poor-charles/Distributed-IoT-Mechatronic-System-for-HVAC-Optimization-using-Hybrid-AI-Logic/Hardware System Files/Data Analysis/Smart_HVAC_Consumer_ROI_Payback.xlsx

Sheet: Consumer Inputs
Smart HVAC Controller Consumer-Side Assumptions
Input | Value | Unit | Purpose / Meanimgng
Electricity Rate | ₱10.5049 | Peso/kWh | Consumer tariff paid for HVAC electricity consumption in Year 1.
Electricity Rate Escalation | 9.0% | %/year | Expected yearly increase in electricity price.
Existing HVAC Annual Energy Consumption (Before Smart Controller) | 2261.15 | kWh/year | Measured or estimated Year 1 annual HVAC energy consumption under manual setpoint operation. The HVAC unit is not purchased; it already exists.
Annual HVAC Energy Consumption Variation | 2.0% | %/year | Expected yearly change in existing HVAC energy use due to weather, occupancy, operating hours, and equipment aging.
Measured Energy Savings Achieved by Smart HVAC Controller | 20.5% | % | Experimentally observed savings delivered by the controller; applied to each year's projected baseline HVAC consumption.
Smart HVAC Controller Package Cost | ₱26000 | Peso | One-time consumer cost for the controller package only. This does NOT include the HVAC unit.
Controller Installation & Setup Cost | ₱0 | Peso | One-time installation, configuration, and commissioning cost for the controller.
Smart Controller Annual Maintenance | ₱1389.4 | Peso/year | Recurring consumer-side operating cost. Enter 0 if none.
Smart Controller Useful Life | 12 | years | Expected service life of the Smart HVAC controller package.
Smart Controller Salvage Value | 0 | Peso | Residual value at the end of the controller useful life for depreciation calculation.

Sheet: Consumer Cash Flow
Consumer Cash Flow: Existing HVAC vs Smart HVAC Controller Purchase
Year | Electricity Rate | Manual HVAC kWh | Smart HVAC kWh | kWh Saved | Manual Bill | Smart Bill | Recurring Smart Cost | Net Annual Savings | Cumulative Net Cash Flow
0 | ₱0.0000 | - | - | - | - | - | - | -₱26000 | -₱26000
1 | ₱10.5049 | 2261.15 | 1796.718835 | 464.4311654 | ₱23753.15463 | ₱18874.35169 | ₱1389.4 | ₱3489.402949 | -₱22510.59705
2 | ₱11.4503 | 2306.373 | 1832.653211 | 473.7197887 | ₱26408.75732 | ₱20984.5042 | ₱1389.4 | ₱4034.853119 | -₱18475.74393
3 | ₱12.4809 | 2352.50046 | 1869.306276 | 483.1941845 | ₱29361.25639 | ₱23330.57177 | ₱1389.4 | ₱4641.284618 | -₱13834.45931
4 | ₱13.6042 | 2399.550469 | 1906.692401 | 492.8580682 | ₱32643.84486 | ₱25938.9297 | ₱1389.4 | ₱5315.515158 | -₱8518.944155
5 | ₱14.8285 | 2447.541479 | 1944.826249 | 502.7152295 | ₱36293.42671 | ₱28838.90204 | ₱1389.4 | ₱6065.124673 | -₱2453.819483
6 | ₱16.1631 | 2496.492308 | 1983.722774 | 512.7695341 | ₱40351.03182 | ₱32063.09129 | ₱1389.4 | ₱6898.540531 | ₱4444.721049
7 | ₱17.6178 | 2546.422154 | 2023.39723 | 523.0249248 | ₱44862.27718 | ₱35647.74489 | ₱1389.4 | ₱7825.132283 | ₱12269.85333
8 | ₱19.2034 | 2597.350597 | 2063.865174 | 533.4854233 | ₱49877.87976 | ₱39633.16277 | ₱1389.4 | ₱8855.316992 | ₱21125.17032
9 | ₱20.9317 | 2649.297609 | 2105.142478 | 544.1551318 | ₱55454.22672 | ₱44064.15037 | ₱1389.4 | ₱10000.67635 | ₱31125.84667
10 | ₱22.8155 | 2702.283562 | 2147.245327 | 555.0382344 | ₱61654.00927 | ₱48990.52238 | ₱1389.4 | ₱11274.08689 | ₱42399.93356
11 | ₱24.8689 | 2756.329233 | 2190.190234 | 566.1389991 | ₱68546.9275 | ₱54467.66278 | ₱1389.4 | ₱12689.86472 | ₱55089.79828
12 | ₱27.1071 | 2811.455817 | 2233.994038 | 577.4617791 | ₱76210.474 | ₱60557.14748 | ₱1389.4 | ₱14263.92652 | ₱69353.7248

Sheet: Consumer Scenarios
Consumer Adoption Scenarios
Scenario | Savings % | Electricity Rate | Year 1 Net Savings | Total CAPEX | Simple Payback | 12-Year ROI
Base | 20.5% | ₱10.50 | ₱3489.402949 | ₱26000 | 7.45 | 61.0%

Sheet: Sensitivity Analysis
Sensitivity Analysis: Payback Under Varying Electricity Rate and Savings
Savings % \ Rate | 8 | 10 | 12 | 14 | 16
2.0% | Not recovered | Not recovered | Not recovered | Not recovered | Not recovered
4.0% | Not recovered | Not recovered | Not recovered | Not recovered | 450.33
6.0% | Not recovered | Not recovered | 108.96 | 50.98 | 33.28
8.0% | 450.33 | 61.98 | 33.28 | 22.75 | 17.28
10.0% | 61.98 | 29.83 | 19.64 | 14.64 | 11.67
12.0% | 33.28 | 19.64 | 13.93 | 10.79 | 8.81

Sheet: Depreciation Schedule
Straight-Line Depreciation of Smart HVAC Controller Package
Year | Annual Depreciation | Accumulated Depreciation | Book Value | Note
0 | ₱0 | ₱0 | ₱26000 | Initial book value of controller asset.
1 | ₱2166.666667 | ₱2166.666667 | ₱23833.33333 | Depreciation is accounting-based and is not deducted from cash savings.
2 | ₱2166.666667 | ₱4333.333333 | ₱21666.66667 | Depreciation is accounting-based and is not deducted from cash savings.
3 | ₱2166.666667 | ₱6500 | ₱19500 | Depreciation is accounting-based and is not deducted from cash savings.
4 | ₱2166.666667 | ₱8666.666667 | ₱17333.33333 | Depreciation is accounting-based and is not deducted from cash savings.
5 | ₱2166.666667 | ₱10833.33333 | ₱15166.66667 | Depreciation is accounting-based and is not deducted from cash savings.
6 | ₱2166.666667 | ₱13000 | ₱13000 | Depreciation is accounting-based and is not deducted from cash savings.
7 | ₱2166.666667 | ₱15166.66667 | ₱10833.33333 | Depreciation is accounting-based and is not deducted from cash savings.
8 | ₱2166.666667 | ₱17333.33333 | ₱8666.666667 | Depreciation is accounting-based and is not deducted from cash savings.
9 | ₱2166.666667 | ₱19500 | ₱6500 | Depreciation is accounting-based and is not deducted from cash savings.
10 | ₱2166.666667 | ₱21666.66667 | ₱4333.333333 | Depreciation is accounting-based and is not deducted from cash savings.
11 | ₱2166.666667 | ₱23833.33333 | ₱2166.666667 | Depreciation is accounting-based and is not deducted from cash savings.
12 | ₱2166.666667 | ₱26000 | ₱0 | Depreciation is accounting-based and is not deducted from cash savings.

Sheet: Methodology Notes
Smart HVAC Controller Consumer-Side Techno-Economic Methodology
Scope | This workbook evaluates the consumer's economic benefit from purchasing the Smart HVAC controller package. It does not include the cost of buying a new HVAC unit, because the controller is installed on an existing HVAC system.
CAPEX | Consumer CAPEX includes the controller package cost, controller installation/setup cost, and optional financing cost. It excludes producer-side costs such as R&D, manufacturing overhead, marketing, and salaries.
OPEX | Consumer OPEX includes recurring costs paid by the consumer after purchase, such as maintenance, cloud service, subscription, software support, or periodic calibration. If no recurring cost exists, enter 0.
Baseline Energy | Existing HVAC Annual Energy Consumption is the Year 1 energy use of the current/manual HVAC operation before installing the controller. This should come from measured data, a calibrated simulation, or a validated digital twin.
Variable kWh | Manual HVAC kWh is allowed to vary annually using the Annual HVAC Energy Consumption Variation input. This accounts for changes in weather, occupancy, operating hours, and equipment aging.
Smart HVAC kWh | Smart HVAC kWh is calculated by applying the measured controller savings percentage to each year's projected manual HVAC kWh. The HVAC unit remains the same; only the control strategy changes.
Net Annual Savings | Net Annual Savings = Manual Bill − Smart Bill − Smart Controller OPEX + Additional Maintenance Savings. This is the cash benefit used for payback and ROI.
Payback | Simple Payback = Total Consumer CAPEX / Year 1 Net Annual Savings. The cash-flow sheet also shows the year when cumulative net cash flow becomes positive.
Discounted Payback | Discounted savings apply the optional discount rate to reflect the time value of money. This is shown as a supporting metric; simple payback and ROI are still reported for consumer readability.
ROI | ROI = (Cumulative Net Savings + Residual Value − Initial CAPEX) / Initial CAPEX. It is shown for 3-year, 5-year, and 10-year consumer ownership periods.
Depreciation | Straight-line depreciation is included only as a supporting accounting indicator for the controller asset. It is not subtracted from cash savings because depreciation is not an actual cash outflow.
Yellow Cells | Yellow cells in the Consumer Inputs sheet are editable assumptions. Formula cells in other sheets should generally not be modified.
Defense Note | The economic story is: the consumer already has an HVAC unit, buys only the smart controller, pays any recurring controller OPEX, and receives savings from reduced HVAC electricity consumption.
