poor-charles/Distributed-IoT-Mechatronic-System-for-HVAC-Optimization-using-Hybrid-AI-Logic/Hardware System Files/Enclosures/Raspberry Pi 5/2_Cover2.sldprt

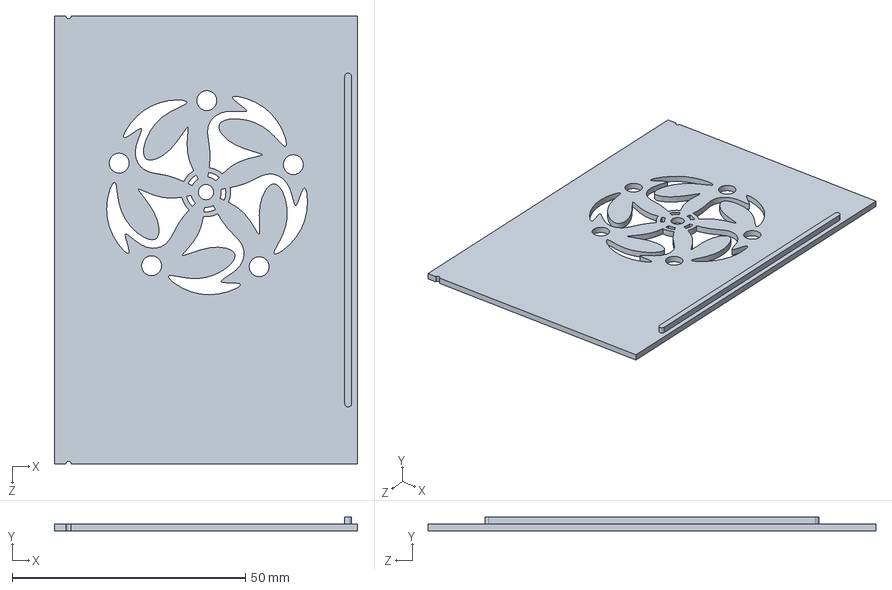
[picture p107: CAD file, 2026-06-13]
Hardware System Files/Enclosures/Raspberry Pi 5/2_Cover2.sldprt
64.9 x 3.00 x 95.9 mm
