poor-charles/Distributed-IoT-Mechatronic-System-for-HVAC-Optimization-using-Hybrid-AI-Logic/Hardware System Files/Enclosures/Temperature Nodes/Sensor Node Cover.SLDPRT

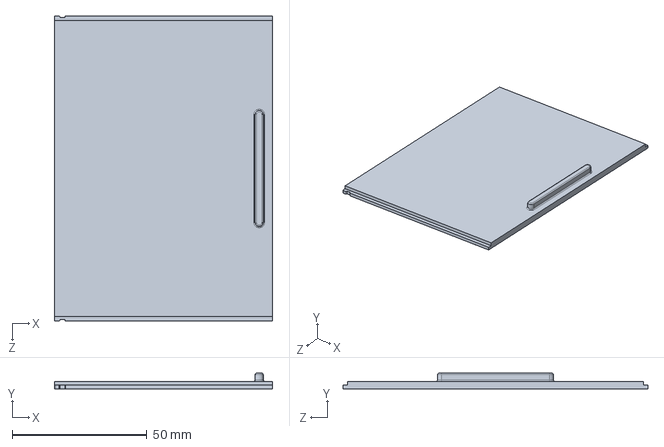
[picture p108: CAD file, 2026-06-13]
Hardware System Files/Enclosures/Temperature Nodes/Sensor Node Cover.SLDPRT
81.0 x 5.80 x 113.1 mm
