poor-charles/Distributed-IoT-Mechatronic-System-for-HVAC-Optimization-using-Hybrid-AI-Logic/Hardware System Files/Enclosures/Raspberry Pi 5/3_Locking2.sldprt

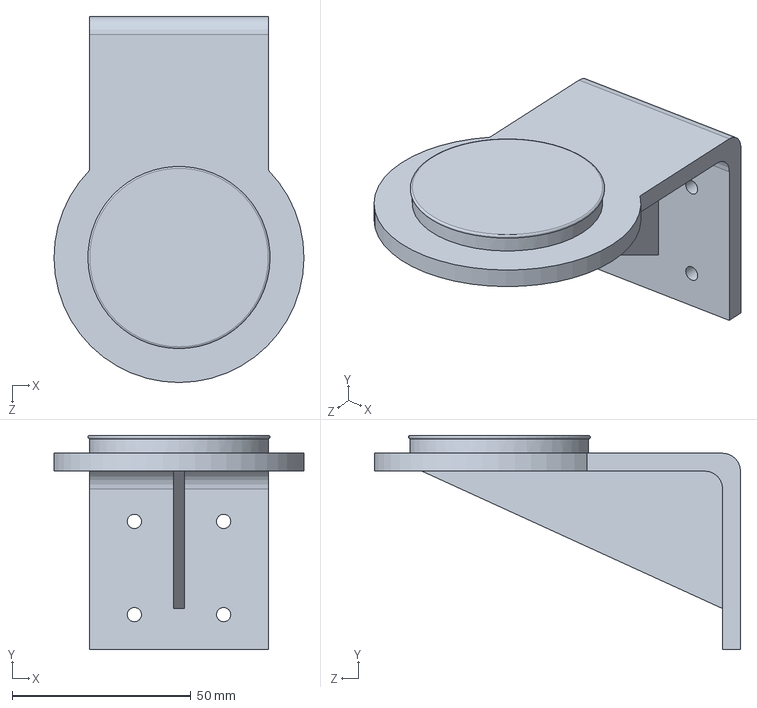
[picture p109: CAD file, 2026-06-13]
Hardware System Files/Enclosures/Raspberry Pi 5/3_Locking2.sldprt
70.0 x 60.0 x 102.5 mm
